ShriyanGote/cse123a-project/Documentation/sections/intro/sustainability_statement.tex

\subsection{Sustainability Statement}

Our project promotes sustainable water consumption habits in shared households. Without knowing the current water level, users often open the fridge only to find an empty filter, leading them to either waste time waiting for it to refill or even use one-time plastic bottles. By providing real-time water level monitoring and low-level alerts, our system encourages refilling and reduces the likelihood of users turning to less sustainable alternatives. Over time, this helps households maintain consistent use of their reusable water filter rather than abandoning it out of frustration.
