ShriyanGote/cse123a-project/Documentation/sections/intro/personas.tex

\subsection{Personas and Users}

\textbf{This is intended for shared households that rely on a shared filtration water container.}

\begin{itemize}
    \item College Roommates
    \begin{itemize}
        \item John Doe, 20 years old, Student at UCSC. John lives in a dorm with two other roommates, and they all rely on a shared water filter for drinking water. Occasionally, John comes out to get water only to find that the water is empty. This creates frustration and delays as John has to choose between missing the bus to refill water or getting to class on time while being thirsty.
    \end{itemize}
    
    \item Family
    \begin{itemize}
        \item Jane Smith, 39 years old, working mother. Jane lives with her husband and two children. Jane gets home after a long, exhausting day of work and is feeling thirsty from the drive home. She goes to the shared water filter to find that it is completely empty. Jane feels frustrated with her stay-at-home husband and two children for not refilling the water filter. This causes her to lash out and yell at them until they all cry, creating a hostile environment in the household.
    \end{itemize}
    
    \item Office
    \begin{itemize}
        \item Joe Micheal, 30 years old, works with Excel spreadsheets. He has very limited time to refill his mug, and his boss, George, never refills the water filter. As a result, Joe's efficiency has substantially decreased at his desk.
    \end{itemize}
\end{itemize}
