ShriyanGote/cse123a-project/Documentation/Poster.pdf

# Introduction

# System Overview

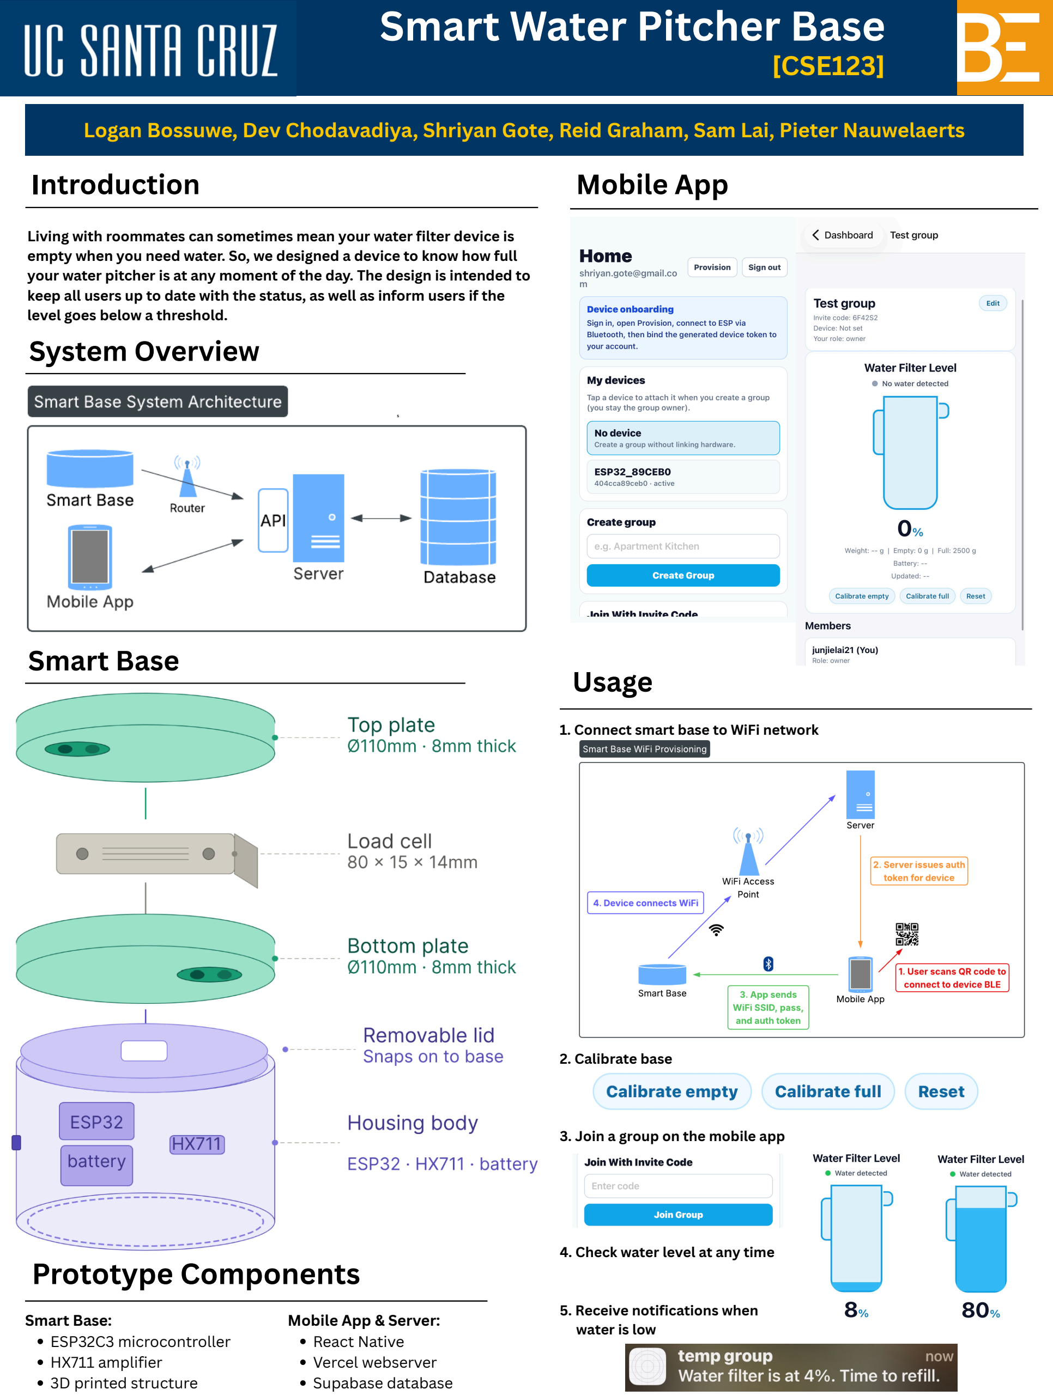
[picture p12: page 1]

Living with roommates can sometimes mean your water filter device is empty when you need water. So, we designed a device to know how full your water pitcher is at any moment of the day. The design is intended to keep all users up to date with the status, as well as inform users if the level goes below a threshold.

S

# Prototype Components

Smart Base:
ESP32C3 microcontroller
HX711 amplifier
3D printed structure

Mobile App & Server:
React Native
Vercel webserver
Supabase database

### 1. Connect smart base to WiFi network

### 2. Calibrate base

### 3. Join a group on the mobile app

### 4. Check water level at any time

### 5. Receive notifications when

water is low

# Usage

# Mobile App

# Smart Water Pitcher Base

# [CSE123]

## Logan Bossuwe, Dev Chodavadiya, Shriyan Gote, Reid Graham, Sam Lai, Pieter Nauwelaerts

# Smart Base
