ShriyanGote/cse123a-project/Documentation/Demo-Script-Q2.pdf

# CSE 123 - Demo Script Smart Water Pitcher Base NOT TURNED IN DONT MAKE IT LOOK GOOD

### Group 8

## Introduction

Presenter: Pieter
Estimated Time: 1.5 minutes
Action: Hold up or gesture toward the water pitcher.

Script:

Sharing a communal water filter can lead to unfortunate moments where you want water, but there is none left in the pitcher. What can be done about this issue? What are the root causes of this problem? And how can we design a solution to reduce the number of times this happens to you.

We all have that one person who returns the filter back empty. They just took a large bottle’s worth of water but didn’t take the time to refill the pitcher for the next person. With this smart base two things will happen. First, you will be able to access an app that tells you how much water is in the pitcher at any given time. This can let you know how much water is in the pitcher at any given time. Second, a notification will alert you if the pitcher is returned with water below 20% full.

With all of these features in mind, how do they work, and how will you the user interact with our product?

## 1 Typical Usage

Presenter: TODO
Estimated Time: TODO

Action: Screen should show app and camera pointed at prototype.

Script:

- screen shows current water lvl

1

- Action: Take out some water
- now it shows the new level
- now i’ll completely empty it
- Action: Empty pitcher
- as you can see the water level updated and everyone in the group rcvd a notification to refill
- Action: Refill pitcher
- and now it shows that its full again

## 2 Account Creation

Presenter: TODO
Estimated Time: TODO

Action: Screen should show app and camera pointed at prototype.

Script:

- create account w email, name etc
- show email verification and verify
- sign in on app

## 3 Provisioning

Presenter: TODO
Estimated Time: TODO

Script:

“When first purchasing product, users need to set up the device. they start by opening app and click setup.”

Action: Open setup page on mobile app

“First scan qr code that comes with the device to connect to it over bluetooth.”

Action: Scan QR code

“Next enter the home wifi name and password, which will be sent to the device along with an auth token so it can communicate with the server.”

Action: Enter WiFi credentials

“Once it is connected, users can create a group and invite other users to it, so they can all see the water level and get notifications when it needs to be refilled.”

## 4 Joining a Group

Presenter: TODO
Estimated Time: TODO

Script:

- open group page
- select device, enter name, and create group
- open group and show current water level
- pour some water out and show it reflects change
- show group code, let other person join, show that they joined on the group page
- textbfhold other phone under camera for other person joining
- empty water filter and show both ppl got the notif
- change group name
- delete group

## 5 Calibration

Presenter: Pieter
Estimated Time: 2 minutes

Script:

- open group
- explain why calibrate
- do empty and full

In order for the product to be useful to every possible customer, a calibration sequence is required when setting it up. This calibration feature is also available at any time if the user purchases a new filter. Setting the calibration requires an empty and a full value. We’ll start with full. First, take the pitcher at a full level and place it on the base. Then navigate through the app to find the calibration buttons. Once the full pitcher is on the scale, press ”Calibrate Full”. Next, pour out the water from the filter until it is all empty. Place the pitcher back on the scale and press ”Calibrate Empty”. Now the levels will be accurate to your specific water filter.

## 6 Webpage

Presenter: TODO
Estimated Time: TODO
Action: Screen should show the webpage open in a browser.

Script:

“Alongside the mobile app, we also have a webpage that users can access from the browser.”

Action: Setup Guide panel

“The webpage hosts our setup guide, so a new user can go through the steps and setup their Smart base. These steps cover from openeing the packaage to having it connected to wifi.”

Action: Open the webpage and sign in

“The second part of thewebpage focuses on account management. Once a user signs in, they come to their account page, where they can see all the groups they are in and all the devices linked to their account. They also have some security features like signing out everywhere and deactiviting their account, in case their phone gets lost or stolen.”

Action: Show signing out everywhere feature

“Clicking on the singing out feature, will sign all devices that are loggged in this account out.”

Action: Show delete account

“Clicking on the delete account button, will delete the account. Once you delete it, it is gone. After that you must create a new account.”
