ShriyanGote/cse123a-project/Documentation/Design.tex

\documentclass[12pt]{article}

% Include all packages and commands
\input{sections/preamble.tex}

\begin{document}

\pagestyle{fancy}
%\maketitle

%==========================
% Custom Title Page
%==========================
\begin{titlepage}
    \centering
    \vspace*{2cm}
    
    % Document Title
    {\Huge \bfseries Smart Water Filter Base \par}
    \vspace{0.5cm}
    {\Large Design Document \par}
    \vspace{2cm}
    % Course Info
    {\Large CSE 123B - Spring 2026 \par}
    \vspace{1cm}
    % Group Info
    {\Large Group 8 \par}
    \vspace{2cm}
    % Contributors
    {\large Contributors:\par}
    \vspace{0.3cm}
    {\large
        Logan Bossuwe \\
        Dev Chodavadiya \\
        Shriyan Gote \\
        Reid Graham \\
        Sam Lai \\
        Pieter Nauwelaerts

    \par}
    \vfill
    % Optional: date
    {\large \today \par}
\end{titlepage}

\fancyfoot{}
\fancyhead{}
\fancyfoot[R]{\thepage}

%%%%%%%%%%%%%%%%%%%%%%%%%%%%%%%%%%%%%%%%%%%%%%%%%%%%
%%%%%%%%%%%%%%%% FRONT MATTER %%%%%%%%%%%%%%%%%%%%%%
%%%%%%%%%%%%%%%%%%%%%%%%%%%%%%%%%%%%%%%%%%%%%%%%%%%%

\pagenumbering{roman}
\input{sections/intro/executive_summary.tex}        
\newpage
\tableofcontents                                    
\newpage

%%%%%%%%%%%%%%%%%%%%%%%%%%%%%%%%%%%%%%%%%%%%%%%%%%%%
%%%%%%%%%%%%%%%%%%%% BODY %%%%%%%%%%%%%%%%%%%%%%%%%%
%%%%%%%%%%%%%%%%%%%%%%%%%%%%%%%%%%%%%%%%%%%%%%%%%%%%

\pagenumbering{arabic}

%%%%%%%%%%%%%%%%%%%% INTRODUCTION (WHY?) %%%%%%%%%%%%%%%%%%%%

\section{Introduction}
\input{sections/intro/problem_statement.tex}
\input{sections/intro/need_statement.tex}
\input{sections/intro/goal_statement.tex}
\input{sections/intro/personas.tex}
\input{sections/intro/research_existing_products.tex}
\input{sections/intro/sustainability_statement.tex}  

%%%%%%%%%%%%%%%%%%%% DESIGN (WHAT?) %%%%%%%%%%%%%%%%%%%%%%%%%

\section{Design}
\input{sections/design/design_objective.tex}
\input{sections/design/aesthetic_prototype.tex}
\input{sections/design/design_for_manufacture.tex}     
\input{sections/design/HX711_code.tex}
\input{sections/design/block_diagrams.tex}             

\input{sections/design/wiring_diagrams.tex}            
\input{sections/design/custom_board.tex}
\input{sections/design/wifi_provisioning.tex}   
\input{sections/design/https_functionality.tex}             
\input{sections/design/web_app.tex}
\input{sections/design/mobile_app.tex}

%\input{sections/design/simulations.tex}                %TODO

%%%%%%%%%%%%%%%%%%%% EVALUATION (WORKS?) %%%%%%%%%%%%%%%%%%%%

\section{Evaluation}
\input{sections/evaluation/testing.tex}                %TODO
\input{sections/evaluation/system_testing.tex}
\input{sections/evaluation/web_app_test.tex}  
\input{sections/evaluation/HX711_test.tex}    

%%%%%%%%%%%%%%%%%%%%%%%%%%%%%%%%%%%%%%%%%%%%%%%%%%%%
%%%%%%%%%%%%%%%%%%%% APPENDICES %%%%%%%%%%%%%%%%%%%%
%%%%%%%%%%%%%%%%%%%%%%%%%%%%%%%%%%%%%%%%%%%%%%%%%%%%

\appendix

%%%%%%%%%%%%%%%%%%%% APPENDIX 1 %%%%%%%%%%%%%%%%%%%%

\section{Problem Formulation}               
\input{sections/appendix1/conceptualizations.tex}       
\input{sections/appendix1/brainstorming.tex}            
\input{sections/appendix1/decision_table.tex}
%\input{sections/appendix1/morphological_charts.tex}     %TODO

%%%%%%%%%%%%%%%%%%%% APPENDIX 2 %%%%%%%%%%%%%%%%%%%%

\section{Planning}                          
\input{sections/appendix2/timeline.tex}
\input{sections/appendix2/division_of_labor.tex}        %TODO
\input{sections/appendix2/collaboration.tex}            %TODO

%%%%%%%%%%%%%%%%%%%% APPENDIX 3 %%%%%%%%%%%%%%%%%%%%

\section{Test Plan \& Results}             
\input{sections/appendix3/testing_plan.tex}

%%%%%%%%%%%%%%%%%%%% APPENDIX 4 %%%%%%%%%%%%%%%%%%%%

\section{Review}                           
\input{sections/appendix4/team_reflections.tex}         %TODO

%%%%%%%%%%%%%%%%%%%%%%%%%%%%%%%%%%%%%%%%%%%%%%%%%%%%

\end{document}
