ShriyanGote/cse123a-project/Documentation/sections/design/block_diagrams.tex

\subsection{Block Diagrams}

\begin{figure}[H]
    \centering
    
    \caption{The system block diagram represents the pieces of the device and design, and how they are interconnected.}
    \end{figure}

% \begin{figure}[H]
%     \centering
%     \includegraphics[width=1.0\textwidth]{Diagrams/Architecture_Diagram.pdf}
%     \caption{The basic architecture of our project, including the modules and submodules of hardware and software, along with how they interact and communicate with each other.}
%     \end{figure}
