ShriyanGote/cse123a-project/Documentation/Diagrams/provisioning_diagram.png

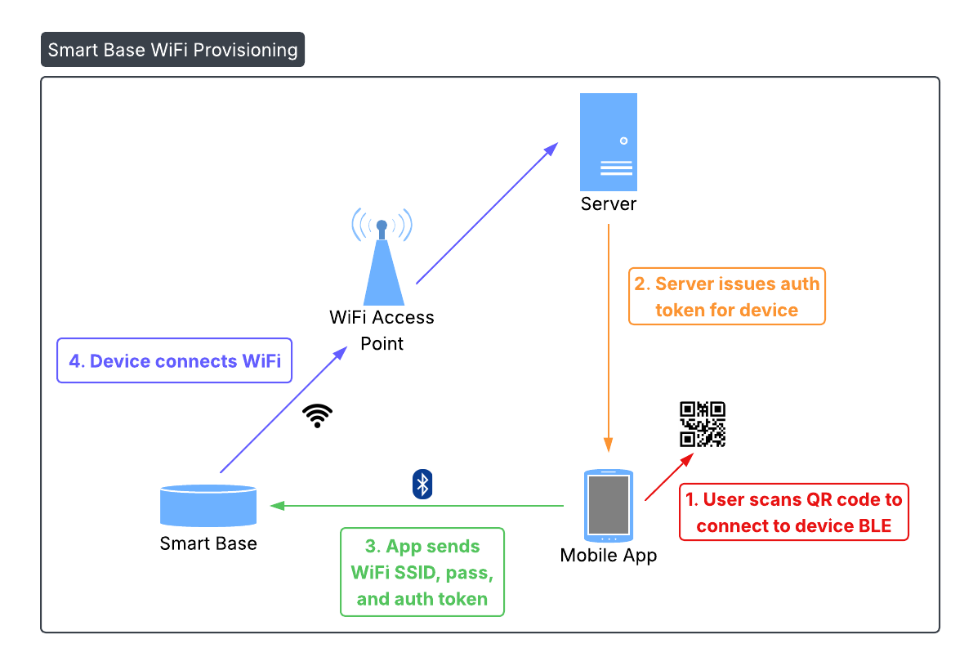
Documentation/Diagrams/provisioning_diagram.png
