ShriyanGote/cse123a-project/Meeting Notes/5_6_communication_diagram.png

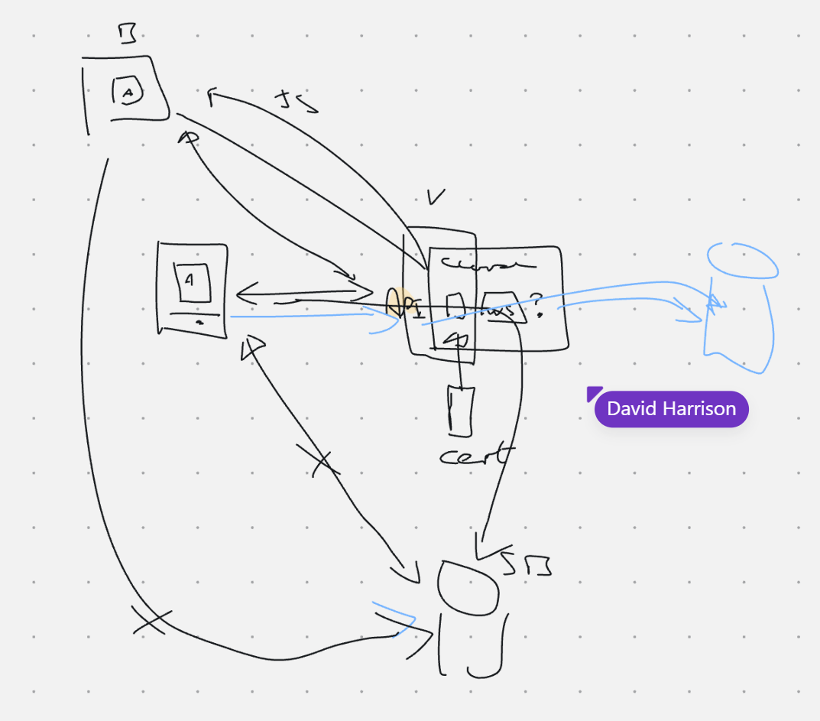
Meeting Notes/5_6_communication_diagram.png
