ShriyanGote/cse123a-project/Meeting Notes/5_6_provisioning_diagram.png

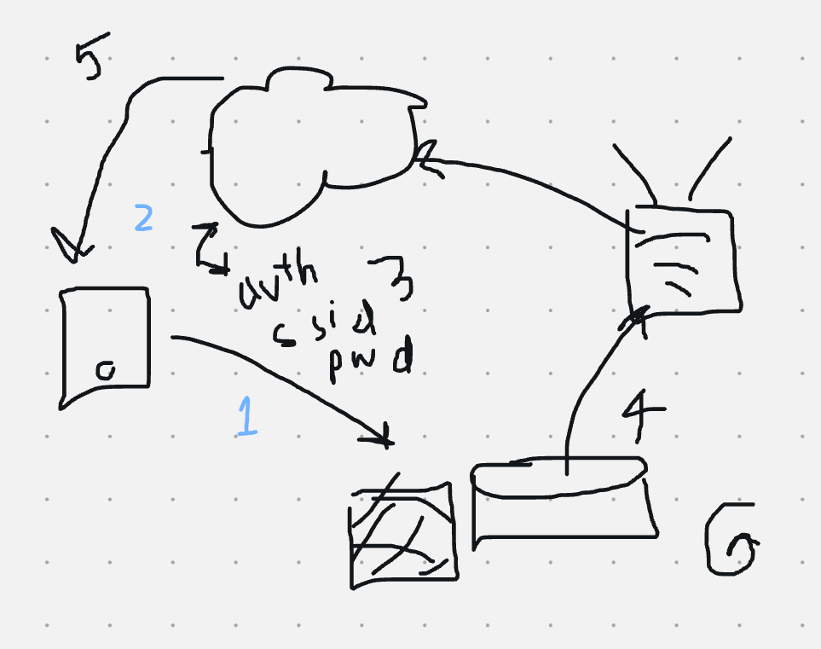
Meeting Notes/5_6_provisioning_diagram.png
