ShriyanGote/cse123a-project/Meeting Notes/IMG_6395.jpeg

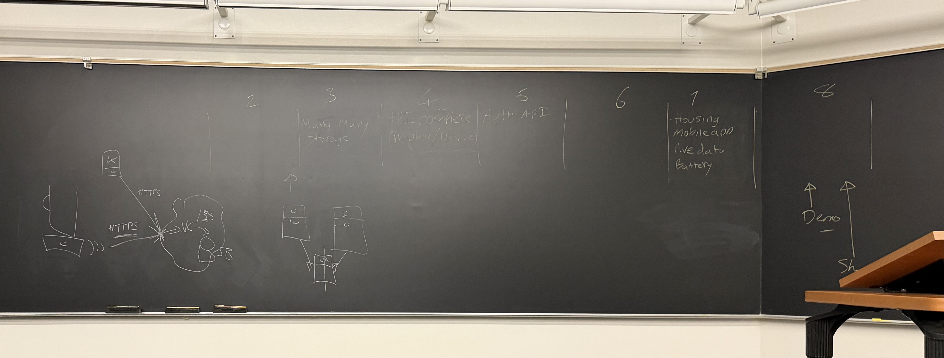
Meeting Notes/IMG_6395.jpeg
