ShriyanGote/cse123a-project/Documentation/Diagrams/Exploded view.pdf

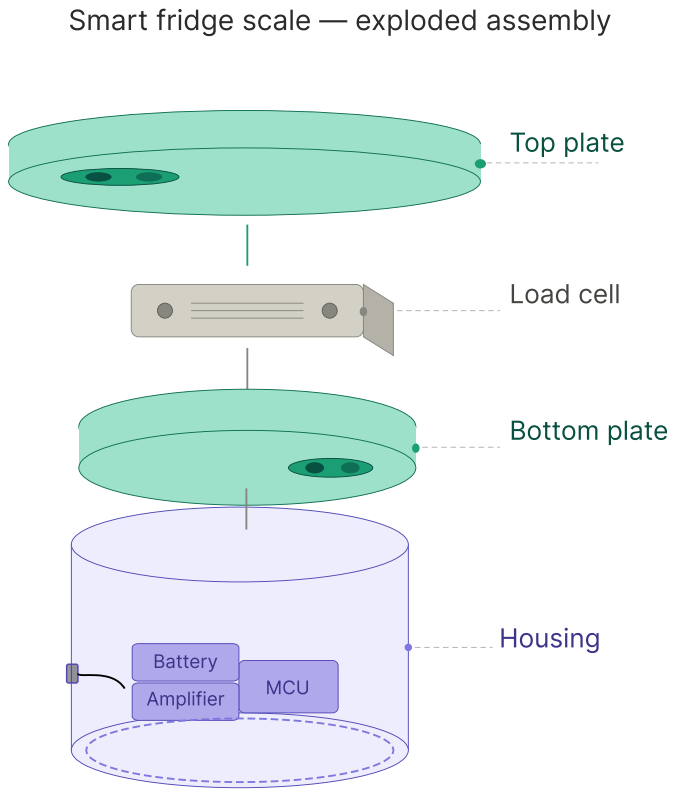
[picture p40: page 1]
Top plate; Load cell; Bottom plate; Battery; Amplifier; MCU; Housing

Smart fridge scale — exploded assembly
