ShriyanGote/cse123a-project/Documentation/Diagrams/Filter-System-Layout.pdf

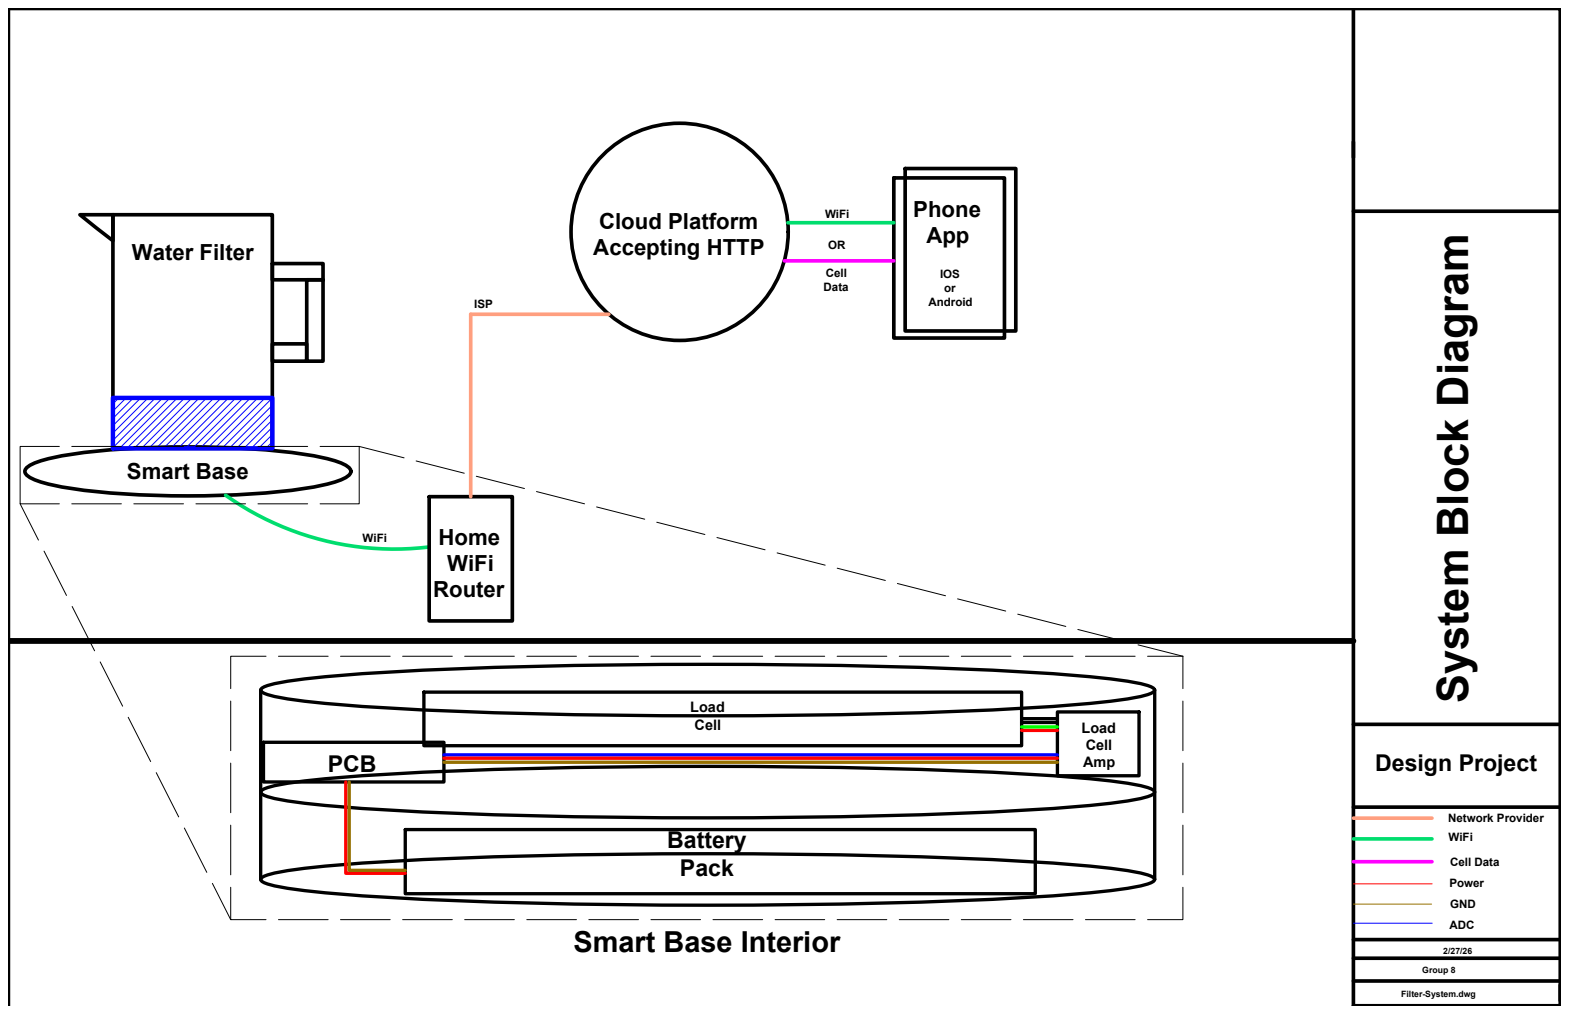
[picture p41: page 1]

System Block Diagram WiFi Design Project 2/27/26 Group 8 Filter-System.dwg Cloud Platform Accepting HTTP Smart Base Water Filter Home WiFi Router Phone App Network Provider Cell Data Smart Base Interior Load Cell Load Cell PCB Amp Battery Pack OR WiFi Cell Data Power GND ADC IOSor Android WiFi ISP
