ShriyanGote/cse123a-project/Documentation/Diagrams/Filter-System-Prototype-Layout 2.pdf

# Cloud Platform Accepting HTTP

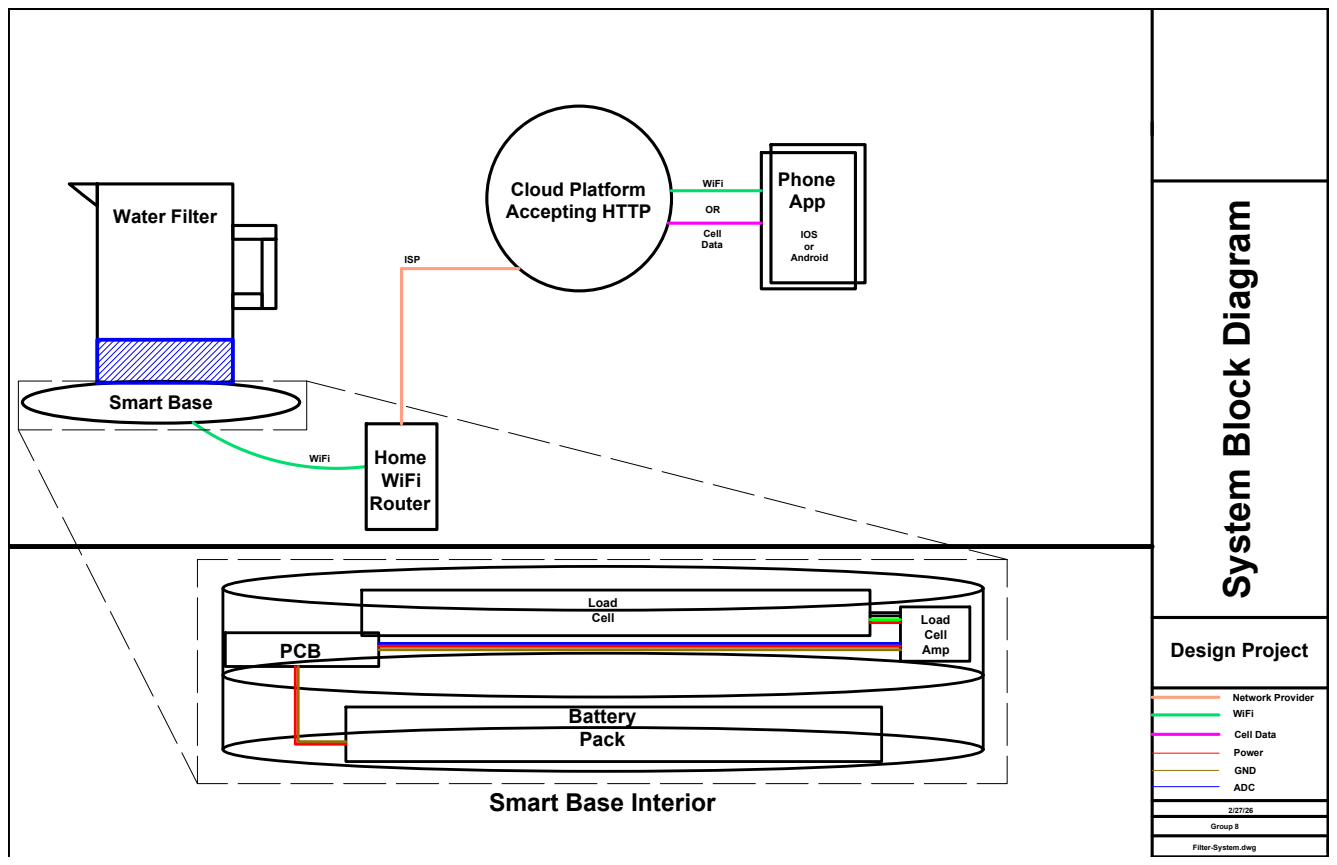
[picture p42: page 1]
WiFi; Design Project; Group 8; Smart Base; Water Filter; Home WiFi Router; Phone App; Network Provider; Cell Data; Load; Cell; PCB; Amp; Battery Pack; Power; GND; ADC; IOS or Android; ISP

System Block Diagram

Smart Base Interior

Filter-System.dwg

# Water Filter

# Laptop

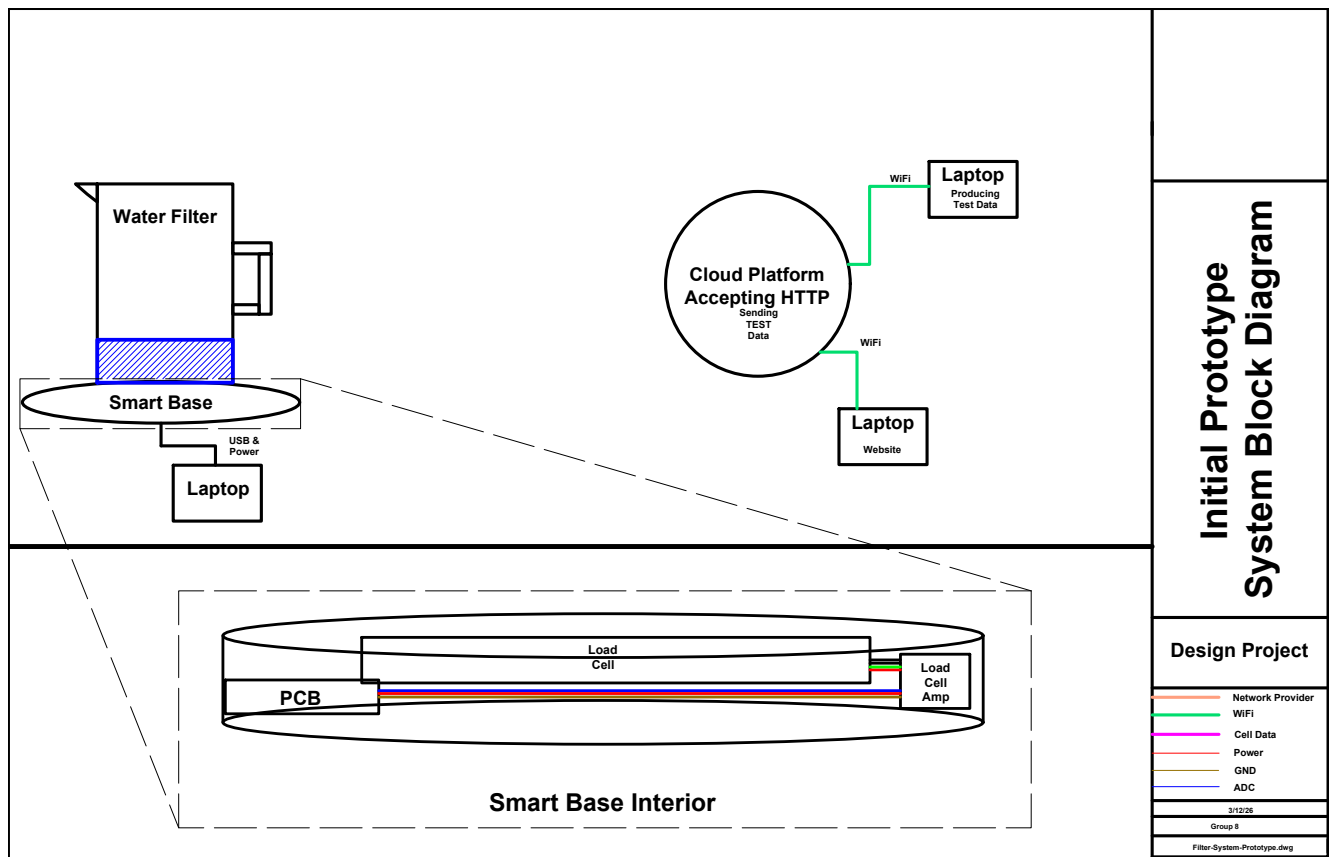
[picture p43: page 2]
Initial Prototype; WiFi; Design Project; Group 8; Cloud Platform Accepting HTTP; Smart Base; Network Provider; Cell Data; Load; Cell; PCB; Amp; Power; GND; ADC; Laptop; USB & Power; Sending TEST Data; Website; Producing Test Data

System Block Diagram

Smart Base Interior

Filter-System-Prototype.dwg
