ShriyanGote/cse123a-project/Documentation/Diagrams/Filter-System-Prototype-Layout.pdf

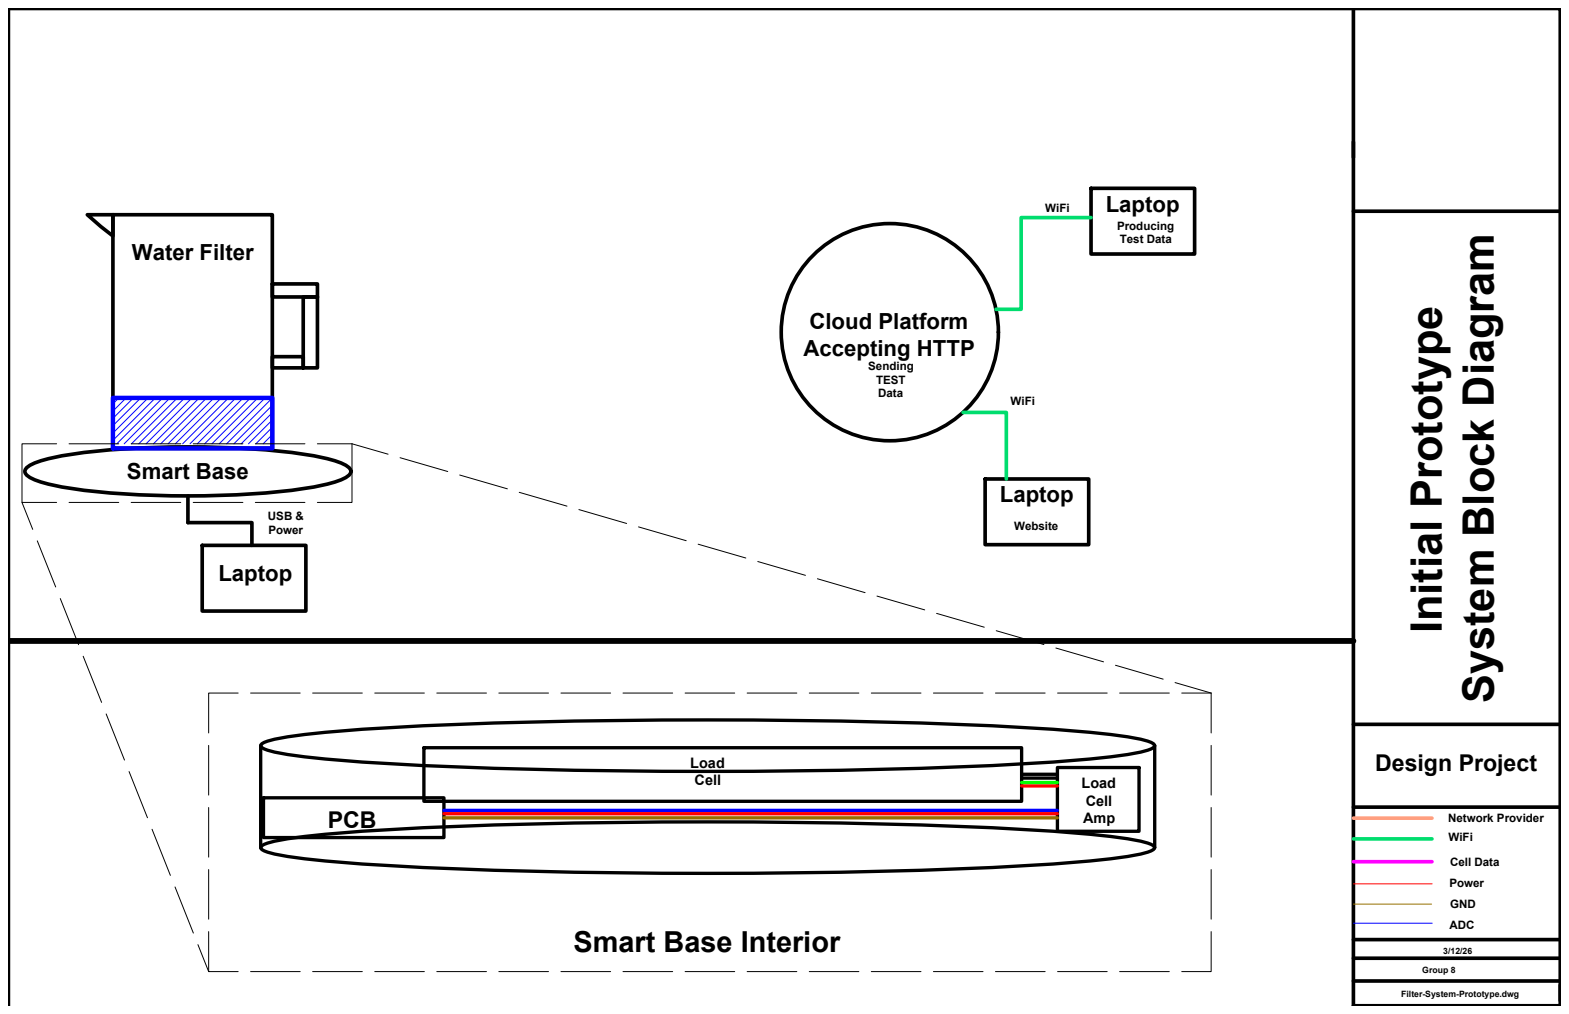
[picture p44: page 1]
Initial Prototype

System Block Diagram WiFi Design Project 3/12/26 Group 8 Filter-System-Prototype.dwg Cloud Platform Accepting HTTP Smart Base Water Filter Network Provider Cell Data Smart Base Interior Load Cell Load Cell PCB Amp Power GND ADC LaptopUSB & Power Sending TEST Data Laptop Website Laptop Producing Test Data WiFi WiFi
