ShriyanGote/cse123a-project/Hardware Notes/PCB Design/Research/esp32-c3-devkit-rust-2-board.pdf

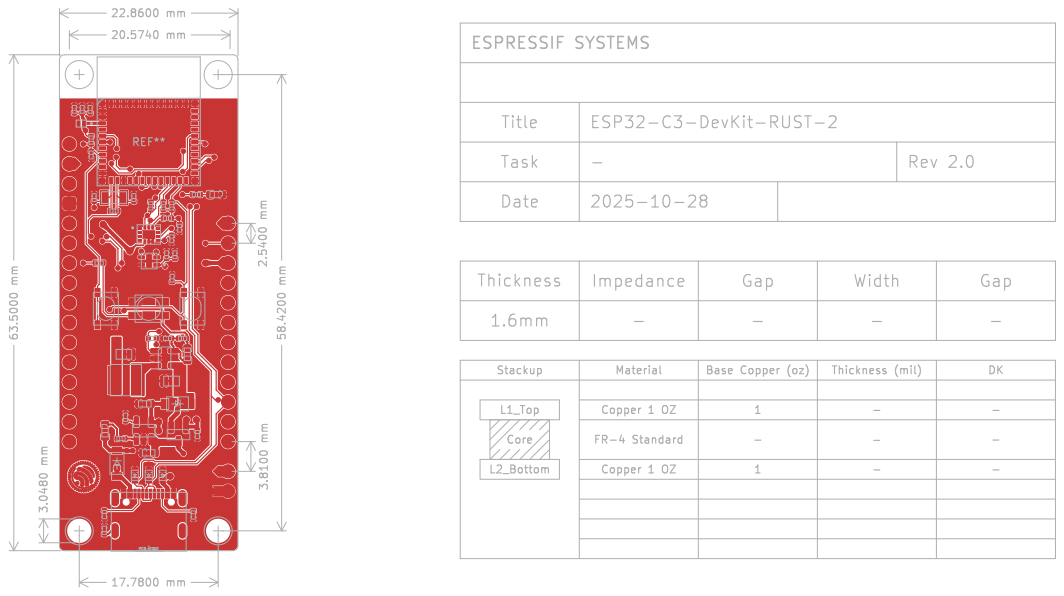
[picture p45: page 1]

ESP32-C3-DevKit-RUST-2 Task

2025-10-28
- Copper 1 OZ | | | DK

- Copper 1 OZ Material Impedance

- Base Copper (oz)

Standard | 1 | - FR-4

File: esp-rust-board.kicad_pcb Sheet: Espressif Systems

Id: 1/6 Title: ESP32-C3-DevKit-RUST-2

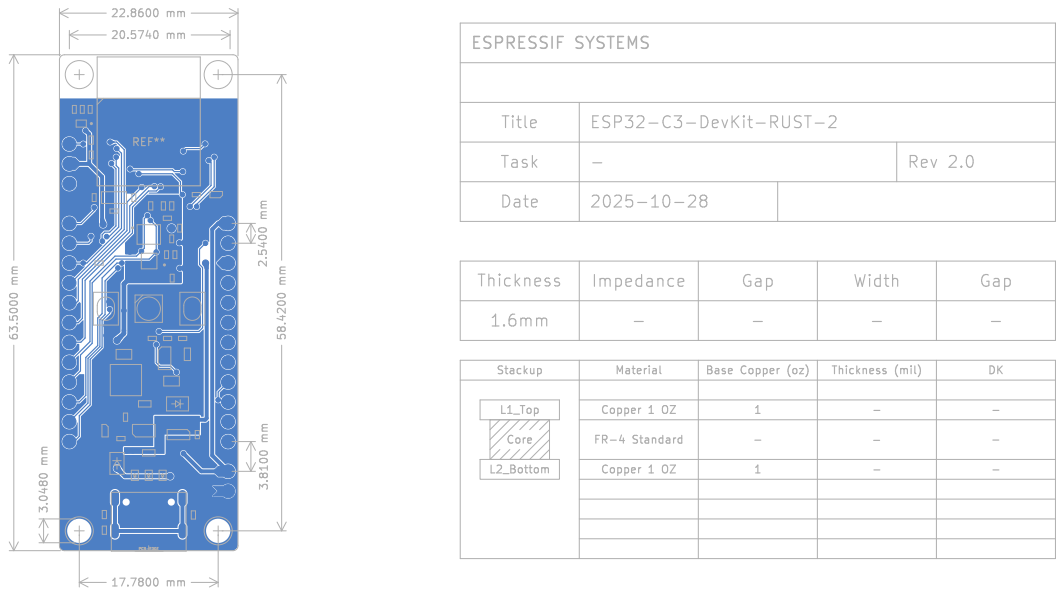
[picture p46: page 2]

- Copper 1 OZ Material Impedance

- Copper 1 OZ | | | DK

- Base Copper (oz)

Standard | 1 | - FR-4

File: esp-rust-board.kicad_pcb Sheet: Espressif Systems

Id: 2/6 Title: ESP32-C3-DevKit-RUST-2

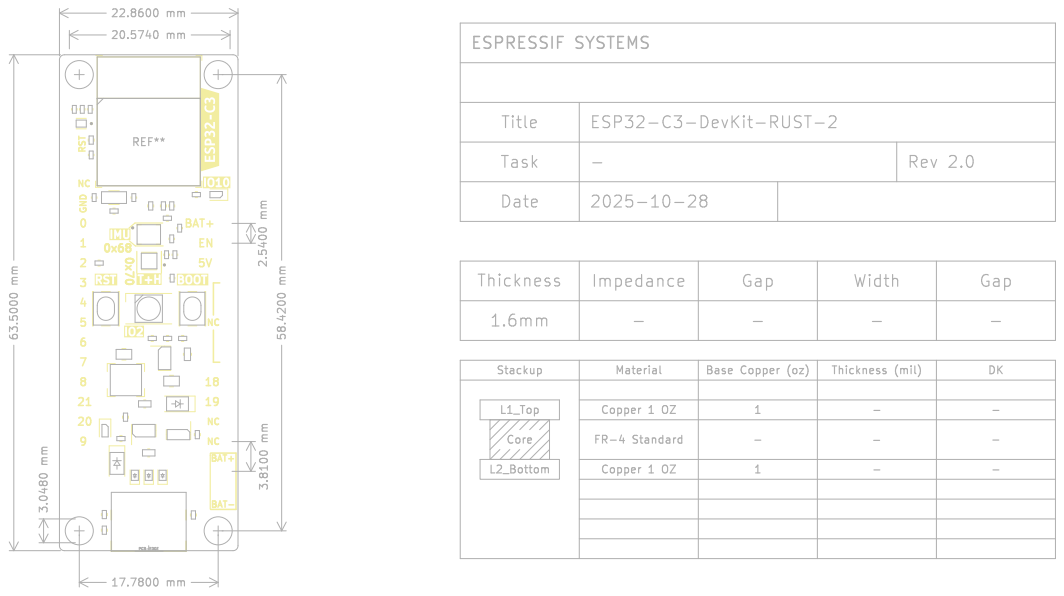
[picture p47: page 3]

- Copper 1 OZ Material Impedance

- Copper 1 OZ | | | DK

- Base Copper (oz)

Standard | 1 | - FR-4

File: esp-rust-board.kicad_pcb Sheet: Espressif Systems

Id: 3/6 Title: ESP32-C3-DevKit-RUST-2

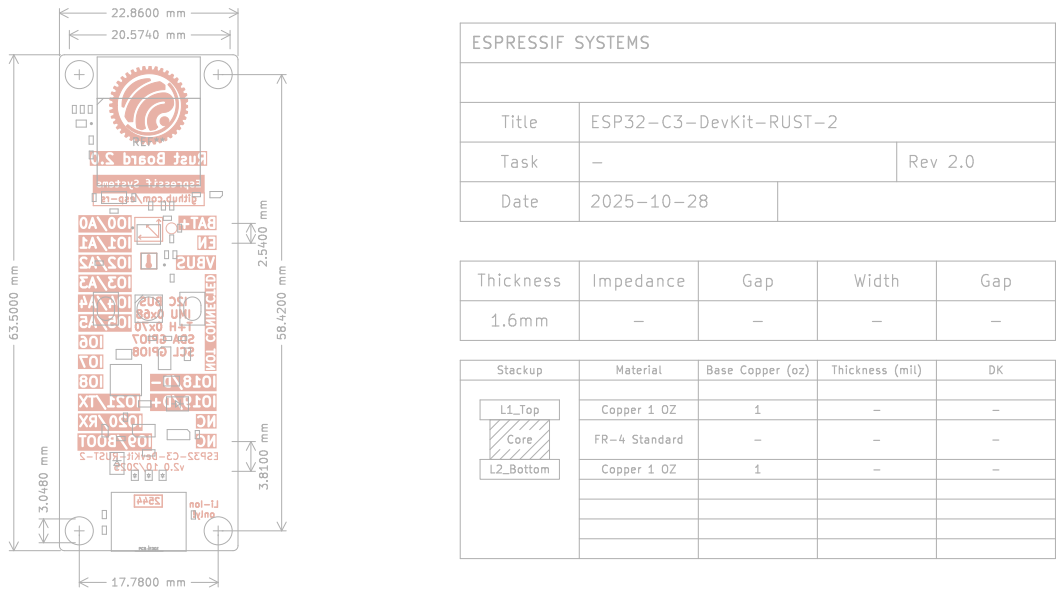
[picture p48: page 4]

- Copper 1 OZ Material Impedance

- Copper 1 OZ | | | DK

- Base Copper (oz)

Standard | 1 | - FR-4

File: esp-rust-board.kicad_pcb Sheet: Espressif Systems

Id: 4/6 Title: ESP32-C3-DevKit-RUST-2

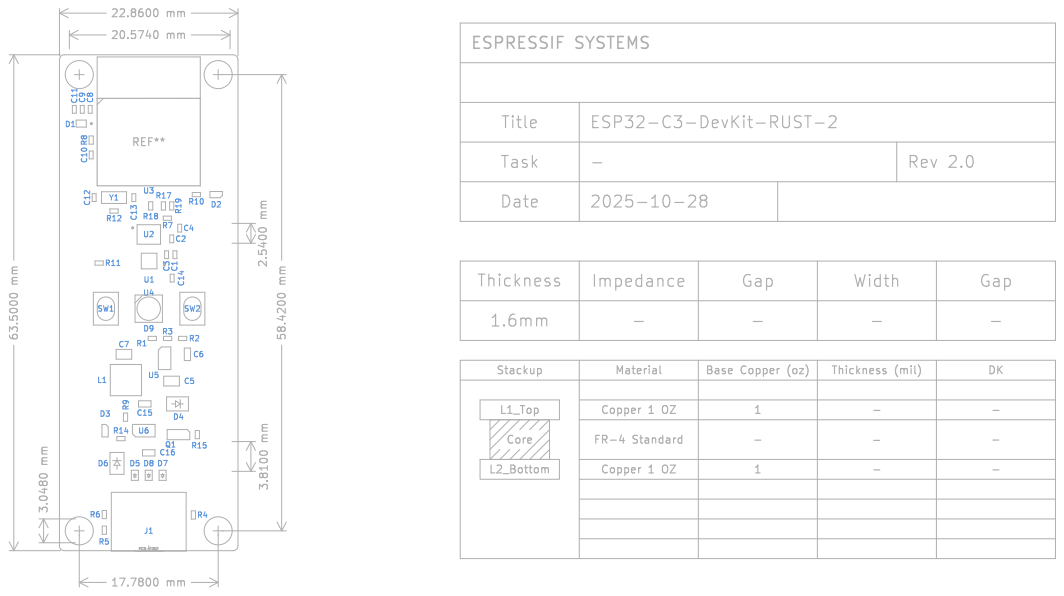
[picture p49: page 5]

- Copper 1 OZ Material Impedance

- Copper 1 OZ | | | DK

- Base Copper (oz)

Standard | 1 | - FR-4

File: esp-rust-board.kicad_pcb Sheet: Espressif Systems

Id: 5/6 Title: ESP32-C3-DevKit-RUST-2

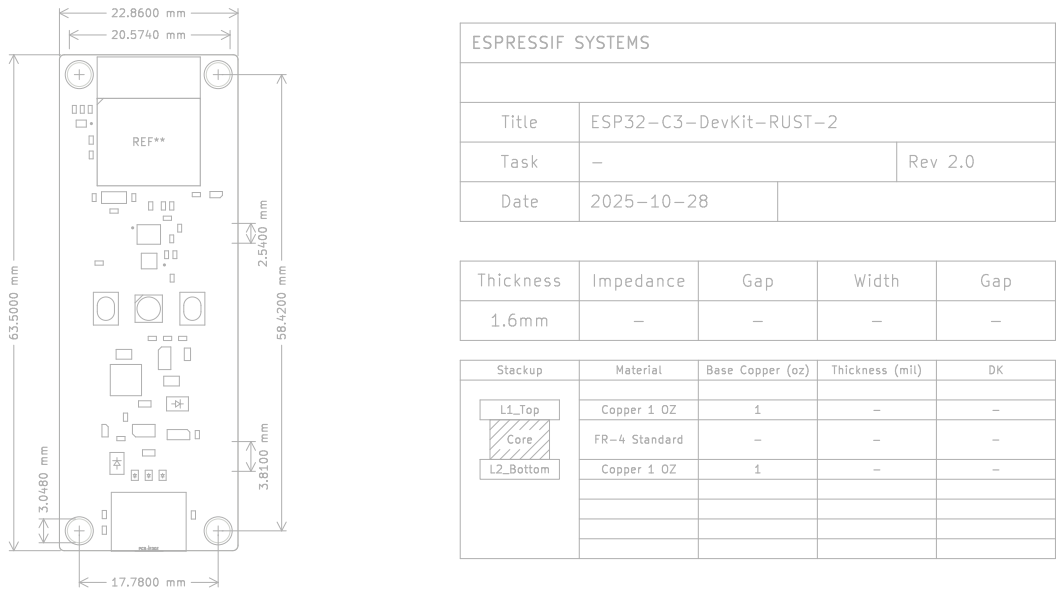
[picture p50: page 6]

- Copper 1 OZ Material Impedance

- Copper 1 OZ | | | DK

- Base Copper (oz)

Standard | 1 | - FR-4

File: esp-rust-board.kicad_pcb Sheet: Espressif Systems

Id: 6/6 Title: ESP32-C3-DevKit-RUST-2
