ShriyanGote/cse123a-project/Code/ESP32/HX711/main/ble.h

#ifndef BLE_PROVISIONING_H
#define BLE_PROVISIONING_H

#include "esp_err.h"

#ifdef __cplusplus
extern "C" {
#endif

esp_err_t ble_provisioning_init(void);

#ifdef __cplusplus
}
#endif

#endif /* BLE_PROVISIONING_H */
