ShriyanGote/cse123a-project/Code/ESP32/HTTPS_testing/main/wifi_manager.c

/**
 * @file wifi_manager.c
 * @brief WiFi connection manager for ESP32
 * 
 * This module handles WiFi initialization and connection management,
 * including event handling for connection state changes.
 */

#include <string.h>
#include "wifi_manager.h"

#include "freertos/FreeRTOS.h"
#include "freertos/event_groups.h"

#include "esp_log.h"
#include "esp_wifi.h"
#include "esp_event.h"
#include "esp_netif.h"
#include "nvs_flash.h"

static const char *TAG = "WIFI";

/* Event group handle for WiFi connection status signaling */
static EventGroupHandle_t wifi_event_group;
#define WIFI_CONNECTED_BIT BIT0

/**
 * @brief WiFi event handler
 * Handles WiFi and IP events, manages connection state and retries
 */
static void event_handler(void *arg,
                          esp_event_base_t event_base,
                          int32_t event_id,
                          void *event_data)
{
    if (event_base == WIFI_EVENT && event_id == WIFI_EVENT_STA_START) {
        esp_wifi_connect();
    }

    if (event_base == WIFI_EVENT && event_id == WIFI_EVENT_STA_DISCONNECTED) {
        ESP_LOGW(TAG, "Disconnected, retrying...");
        esp_wifi_connect();
    }

    if (event_base == IP_EVENT && event_id == IP_EVENT_STA_GOT_IP) {
        ESP_LOGI(TAG, "Got IP");
        xEventGroupSetBits(wifi_event_group, WIFI_CONNECTED_BIT);
    }
}

esp_err_t wifi_init(void)
{
    wifi_event_group = xEventGroupCreate();

    ESP_ERROR_CHECK(nvs_flash_init());
    ESP_ERROR_CHECK(esp_netif_init());
    ESP_ERROR_CHECK(esp_event_loop_create_default());

    esp_netif_create_default_wifi_sta();

    wifi_init_config_t cfg = WIFI_INIT_CONFIG_DEFAULT();
    ESP_ERROR_CHECK(esp_wifi_init(&cfg));

    ESP_ERROR_CHECK(esp_event_handler_register(WIFI_EVENT,
                                               ESP_EVENT_ANY_ID,
                                               &event_handler,
                                               NULL));

    ESP_ERROR_CHECK(esp_event_handler_register(IP_EVENT,
                                               IP_EVENT_STA_GOT_IP,
                                               &event_handler,
                                               NULL));

    return ESP_OK;
}

esp_err_t wifi_connect(const char *ssid, const char *password)
{
    wifi_config_t wifi_config = {0};

    strncpy((char *)wifi_config.sta.ssid, ssid, sizeof(wifi_config.sta.ssid));
    strncpy((char *)wifi_config.sta.password, password, sizeof(wifi_config.sta.password));

    ESP_ERROR_CHECK(esp_wifi_set_mode(WIFI_MODE_STA));
    ESP_ERROR_CHECK(esp_wifi_set_config(WIFI_IF_STA, &wifi_config));
    ESP_ERROR_CHECK(esp_wifi_start());

    ESP_LOGI(TAG, "Connecting to WiFi...");

    return ESP_OK;
}

void wifi_wait_connected(void)
{
    xEventGroupWaitBits(wifi_event_group,
                        WIFI_CONNECTED_BIT,
                        false,
                        true,
                        portMAX_DELAY);

    ESP_LOGI(TAG, "WiFi connected!");
}
